tamercos/PiCycle-S.E.A.T./Prototyping and Progress Images/Busy Hands.jpeg

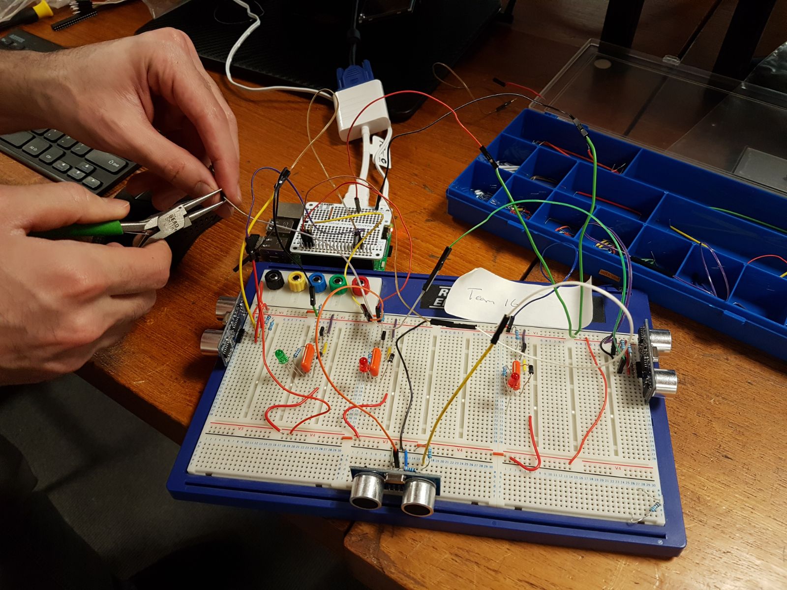
Prototyping and Progress Images/Busy Hands.jpeg
