tamercos/PiCycle-S.E.A.T./Prototyping and Progress Images/Better 3D Print.jpeg

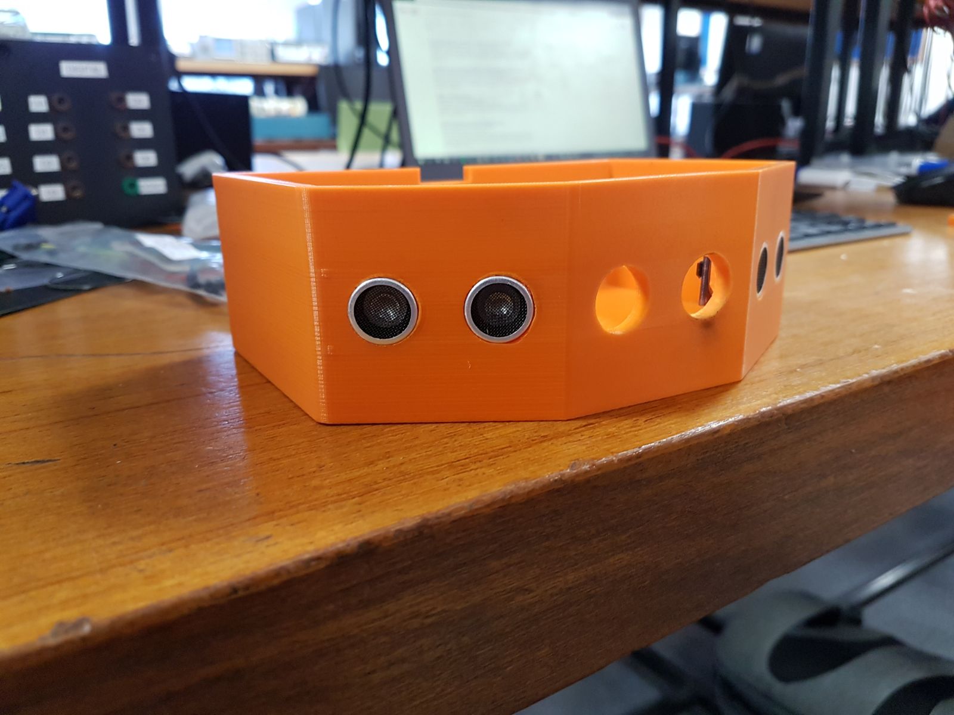
Prototyping and Progress Images/Better 3D Print.jpeg
