tamercos/PiCycle-S.E.A.T./Prototyping and Progress Images/whoops... First 3D Print Attempt.jpeg

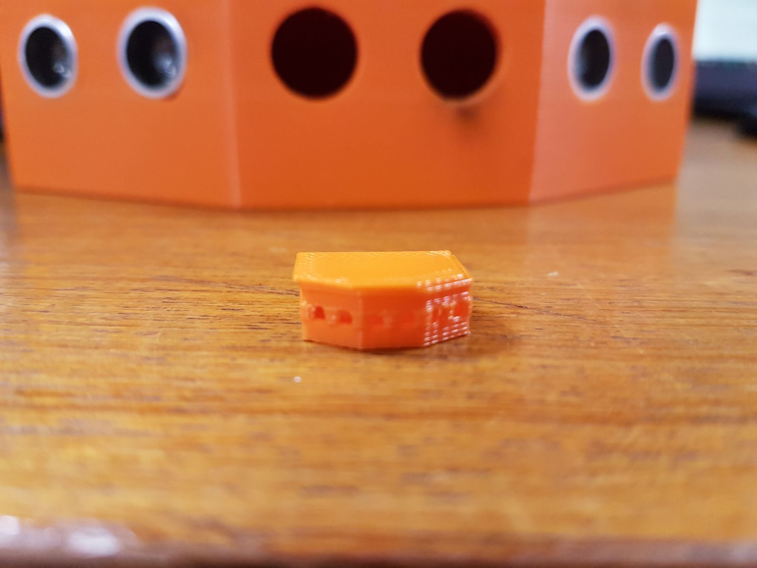
Prototyping and Progress Images/whoops... First 3D Print Attempt.jpeg
