tamercos/PiCycle-S.E.A.T./Program Code/moc_mainwindow.cpp

/****************************************************************************
** Meta object code from reading C++ file 'mainwindow.h'
**
** Created by: The Qt Meta Object Compiler version 63 (Qt 4.8.7)
**
** WARNING! All changes made in this file will be lost!
*****************************************************************************/

#include "mainwindow.h"
#if !defined(Q_MOC_OUTPUT_REVISION)
#error "The header file 'mainwindow.h' doesn't include <QObject>."
#elif Q_MOC_OUTPUT_REVISION != 63
#error "This file was generated using the moc from 4.8.7. It"
#error "cannot be used with the include files from this version of Qt."
#error "(The moc has changed too much.)"
#endif

QT_BEGIN_MOC_NAMESPACE
static const uint qt_meta_data_MainWindow[] = {

 // content:
       6,       // revision
       0,       // classname
       0,    0, // classinfo
       4,   14, // methods
       0,    0, // properties
       0,    0, // enums/sets
       0,    0, // constructors
       0,       // flags
       0,       // signalCount

 // slots: signature, parameters, type, tag, flags
      11,   30,   40,   40, 0x0a,
      41,   60,   40,   40, 0x0a,
      70,   89,   40,   40, 0x0a,
      99,  119,   40,   40, 0x0a,

       0        // eod
};

static const char qt_meta_stringdata_MainWindow[] = {
    "MainWindow\0setVibInput1(bool)\0vibInput1\0"
    "\0setVibInput2(bool)\0vibInput2\0"
    "setVibInput3(bool)\0vibInput3\0"
    "setDetectRange(int)\0detectRange\0"
};

void MainWindow::qt_static_metacall(QObject *_o, QMetaObject::Call _c, int _id, void **_a)
{
    if (_c == QMetaObject::InvokeMetaMethod) {
        Q_ASSERT(staticMetaObject.cast(_o));
        MainWindow *_t = static_cast<MainWindow *>(_o);
        switch (_id) {
        case 0: _t->setVibInput1((*reinterpret_cast< bool(*)>(_a[1]))); break;
        case 1: _t->setVibInput2((*reinterpret_cast< bool(*)>(_a[1]))); break;
        case 2: _t->setVibInput3((*reinterpret_cast< bool(*)>(_a[1]))); break;
        case 3: _t->setDetectRange((*reinterpret_cast< int(*)>(_a[1]))); break;
        default: ;
        }
    }
}

const QMetaObjectExtraData MainWindow::staticMetaObjectExtraData = {
    0,  qt_static_metacall 
};

const QMetaObject MainWindow::staticMetaObject = {
    { &QWidget::staticMetaObject, qt_meta_stringdata_MainWindow,
      qt_meta_data_MainWindow, &staticMetaObjectExtraData }
};

#ifdef Q_NO_DATA_RELOCATION
const QMetaObject &MainWindow::getStaticMetaObject() { return staticMetaObject; }
#endif //Q_NO_DATA_RELOCATION

const QMetaObject *MainWindow::metaObject() const
{
    return QObject::d_ptr->metaObject ? QObject::d_ptr->metaObject : &staticMetaObject;
}

void *MainWindow::qt_metacast(const char *_clname)
{
    if (!_clname) return 0;
    if (!strcmp(_clname, qt_meta_stringdata_MainWindow))
        return static_cast<void*>(const_cast< MainWindow*>(this));
    return QWidget::qt_metacast(_clname);
}

int MainWindow::qt_metacall(QMetaObject::Call _c, int _id, void **_a)
{
    _id = QWidget::qt_metacall(_c, _id, _a);
    if (_id < 0)
        return _id;
    if (_c == QMetaObject::InvokeMetaMethod) {
        if (_id < 4)
            qt_static_metacall(this, _c, _id, _a);
        _id -= 4;
    }
    return _id;
}
QT_END_MOC_NAMESPACE
