tamercos/PiCycle-S.E.A.T./Program Code/libSonar.cpp

#include <iostream>
#include <wiringPi.h>
#include "libSonar.h"

Sonar::Sonar(){

    wiringPiSetup();
    init(trigger1, echo1, vibDisc1, trigger2, echo2, vibDisc2, trigger3, echo3, vibDisc3);

}

void Sonar::init(int trigger1, int echo1, int vibDisc1, int trigger2, int echo2, int vibDisc2,int trigger3, int echo3, int vibDisc3)
{
    this->trigger1=trigger1;
    this->echo1=echo1;
    this->trigger2=trigger2;
    this->echo2=echo2;
    this->trigger3=trigger3;
    this->echo3=echo3;

    pinMode(trigger1, OUTPUT);			//defining trigger, echo and motor pins as input or output
    pinMode(echo1, INPUT);
    pinMode(vibDisc1, OUTPUT);
    pinMode(trigger2, OUTPUT);
    pinMode(echo2, INPUT);
    pinMode(vibDisc2, OUTPUT);
    pinMode(trigger3, OUTPUT);
    pinMode(echo3, INPUT);
    pinMode(vibDisc3, OUTPUT);

    digitalWrite(trigger1, LOW);		//ensuring trigger and motor outputs start in inactive state
    digitalWrite(trigger2, LOW);
    digitalWrite(trigger3, LOW);
    digitalWrite(vibDisc1, LOW);
    digitalWrite(vibDisc2, LOW);
    digitalWrite(vibDisc3, LOW);
    delay(500);
}


//getters for private variables
int Sonar::getVibDisc1(){
    return(vibDisc1);
}
int Sonar::getVibDisc2(){
    return(vibDisc2);
}
int Sonar::getVibDisc3(){
    return(vibDisc3);
}


/**NOTE: 1 second assigned to each sensor in code will result in 6 second accumulative real time for each sample.
        This is because each sensors has one trasmitter and one receiver, so three sensors will have a total of 6 processes.
        i.e. 166667us will result in 1Hz sample rate, 3333us timeout will result in 50Hz sample rate*/

/**************************************
 * Distance Measurement for 1st Sonar *
 **************************************/
void Sonar::recordPulseLength1()
{
    startTimeUsec1 = micros();
    while ( digitalRead(echo1) == HIGH );
    endTimeUsec1 = micros();
}

double Sonar::distance1(int timeout1)
{
    digitalWrite(trigger1, HIGH);
    delayMicroseconds(3333);			//50 Hz sample rate
    digitalWrite(trigger1, LOW);

    now1=micros();

    while (digitalRead(echo1) == LOW && micros() - now1 < timeout1);
    recordPulseLength1();

    travelTimeUsec1 = endTimeUsec1 - startTimeUsec1;
    distanceMeters1 = 100*((travelTimeUsec1/1000000.0)*340.29)/2;           //dist = speed*time converted to cm, where total dist is divided by 2
                                                                            //since sonar wave travels a distance, then travels back to sonar
    return distanceMeters1;
}

/**************************************
 * Distance Measurement for 2nd Sonar *
 **************************************/
void Sonar::recordPulseLength2()
{
    startTimeUsec2 = micros();
    while ( digitalRead(echo2) == HIGH );
    endTimeUsec2 = micros();
}

double Sonar::distance2(int timeout2)
{
    digitalWrite(trigger2, HIGH);
    delayMicroseconds(3333);			//50 Hz sample rate
    digitalWrite(trigger2, LOW);

    now2=micros();

    while (digitalRead(echo2) == LOW && micros() - now2 < timeout2);
    recordPulseLength2();

    travelTimeUsec2 = endTimeUsec2 - startTimeUsec2;
    distanceMeters2 = 100*((travelTimeUsec2/1000000.0)*340.29)/2;
    
    return distanceMeters2;
}

/**************************************
 * Distance Measurement for 3rd Sonar *
 **************************************/
void Sonar::recordPulseLength3()
{
    startTimeUsec3 = micros();
    while ( digitalRead(echo3) == HIGH );
    endTimeUsec3 = micros();
}

double Sonar::distance3(int timeout3)
{
    digitalWrite(trigger3, HIGH);
    delayMicroseconds(3333);			//50 Hz sample rate
    digitalWrite(trigger3, LOW);

    now3=micros();

    while (digitalRead(echo3) == LOW && micros() - now3 < timeout3);
    recordPulseLength3();

    travelTimeUsec3 = endTimeUsec3 - startTimeUsec3;
    distanceMeters3 = 100*((travelTimeUsec3/1000000.0)*340.29)/2;


    return distanceMeters3;
}
