tamercos/PiCycle-S.E.A.T./libSonar.h

#ifndef DEF_SONAR
#define DEF_SONAR

class Sonar
{
  public:
    Sonar();
    void init(int trigger1, int echo1, int motor1, int trigger2, int echo2, int motor2, int trigger3, int echo3, int motor3);
    double distance1(int timeout1);
    double distance2(int timeout2);
    double distance3(int timeout3);

  private:
    void recordPulseLength1();
    void recordPulseLength2();
    void recordPulseLength3();
    int trigger1;
    int echo1;
    int trigger2;
    int echo2;
    int trigger3;
    int echo3;
    int motor1;
    int motor2;
    int motor3;
    int detectRange;
    volatile long startTimeUsec1;
    volatile long startTimeUsec2;
    volatile long startTimeUsec3;
    volatile long endTimeUsec1;
    volatile long endTimeUsec2;
    volatile long endTimeUsec3;
    double distanceMeters1;
    double distanceMeters2;
    double distanceMeters3;
    long travelTimeUsec1;
    long travelTimeUsec2;
    long travelTimeUsec3;
    long now1;
    long now2;
    long now3;
};

#endif
